dockwerk/filterholder/17636/holder_02.jpg

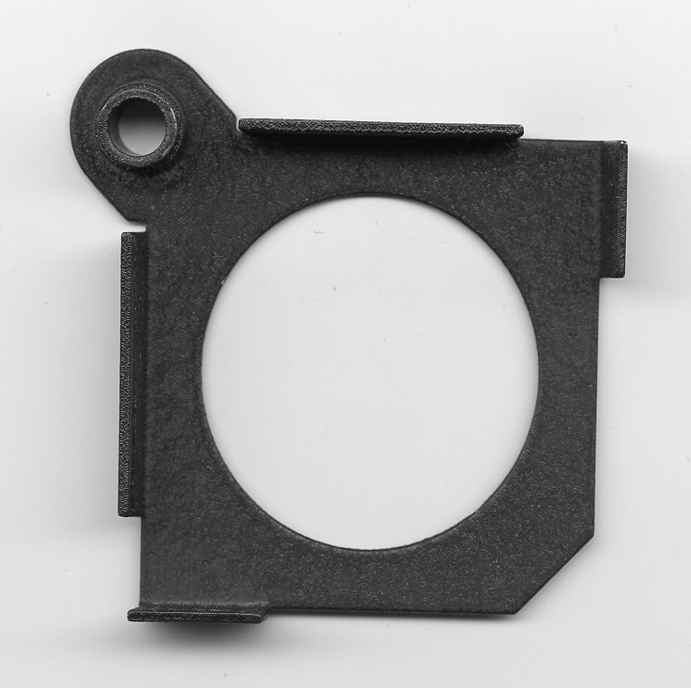
17636/holder_02.jpg
