dockwerk/filterholder/17636/holder_screw_correct.jpg

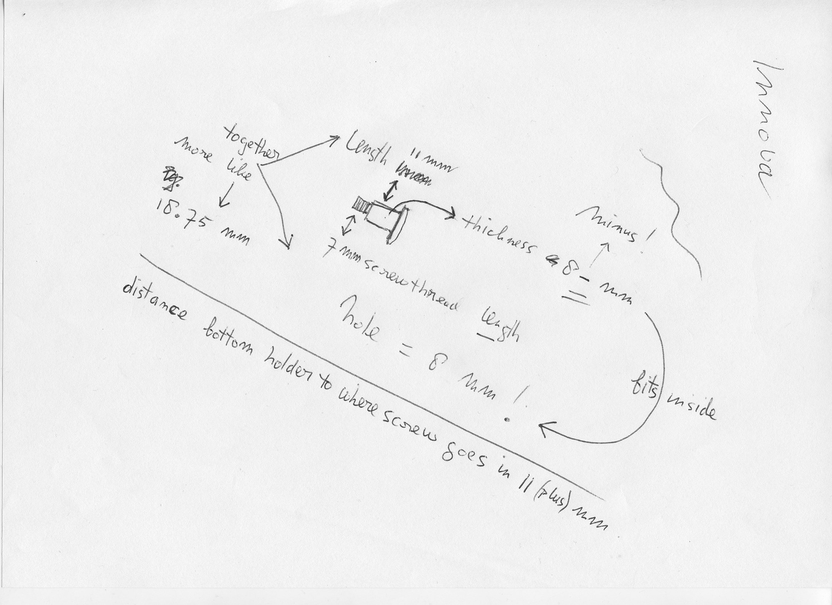
17636/holder_screw_correct.jpg
