dockwerk/filterholder/17636/holder_with_screw.jpg

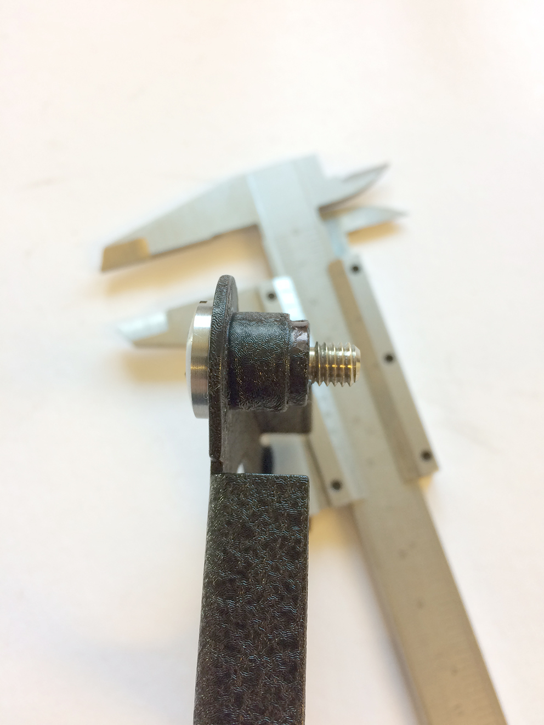
17636/holder_with_screw.jpg
