dockwerk/filterholder/prototypes/DSC_9276.jpg

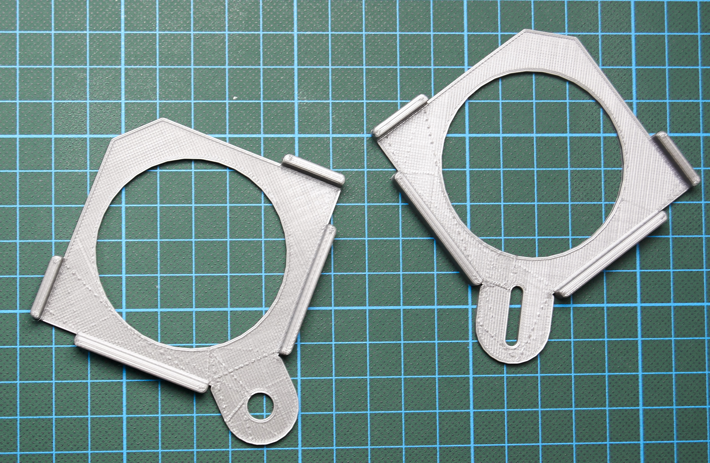
prototypes/DSC_9276.jpg
