dockwerk/filterholder/prototypes/DSC_9277.jpg

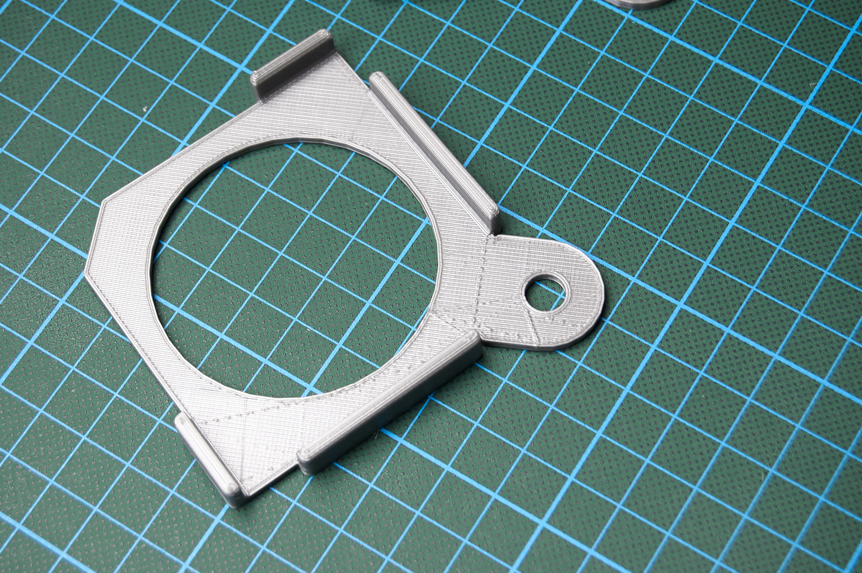
prototypes/DSC_9277.jpg
