dockwerk/filterholder/prototypes/DSC_9278.jpg

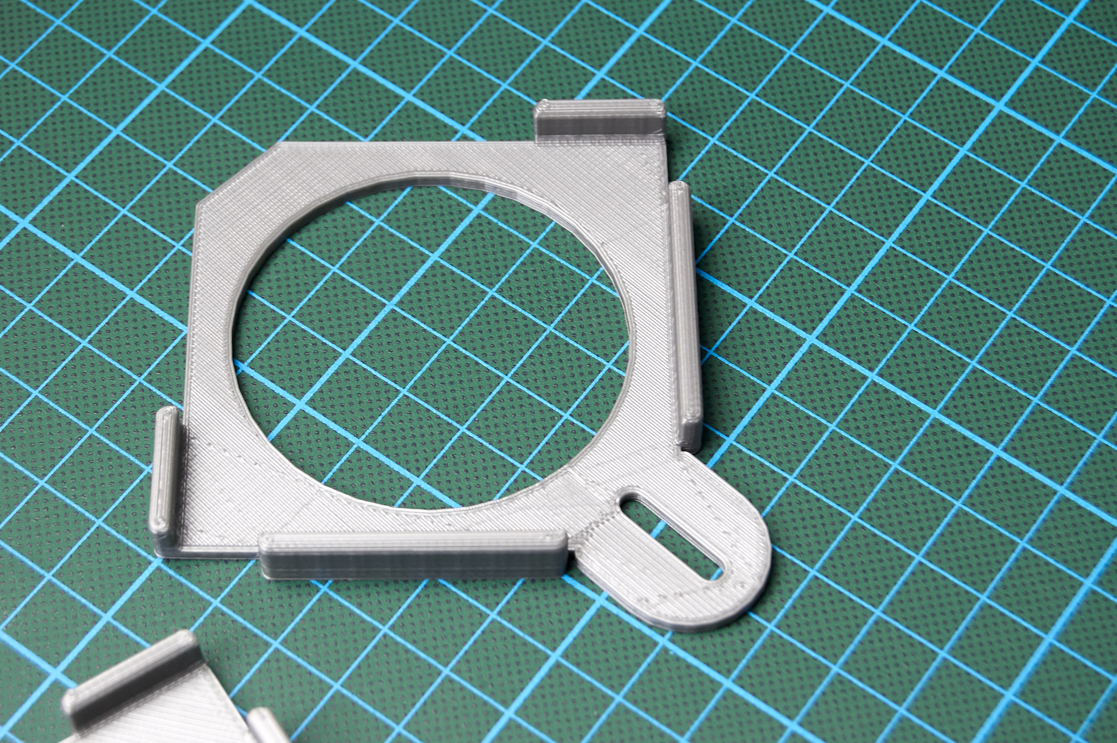
prototypes/DSC_9278.jpg
