dockwerk/filterholder/prototypes/DSC_9281.jpg

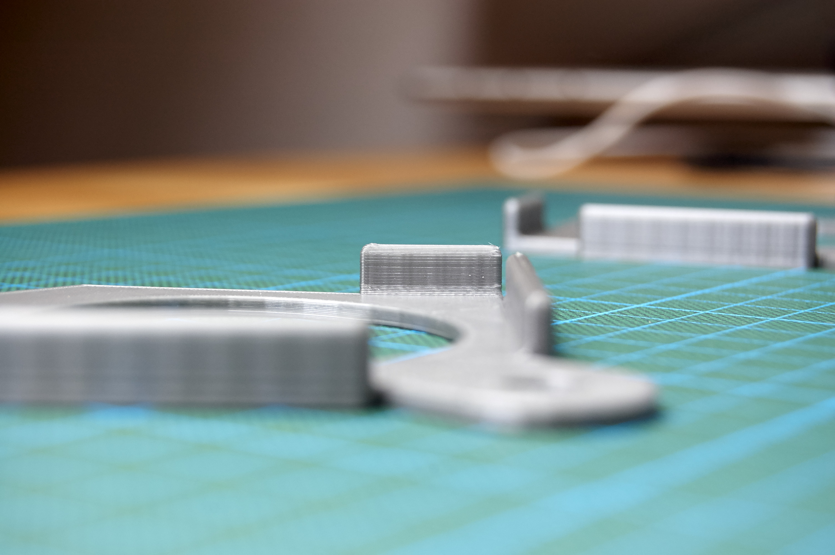
prototypes/DSC_9281.jpg
