dockwerk/filterholder/prototypes/DSC_9283.jpg

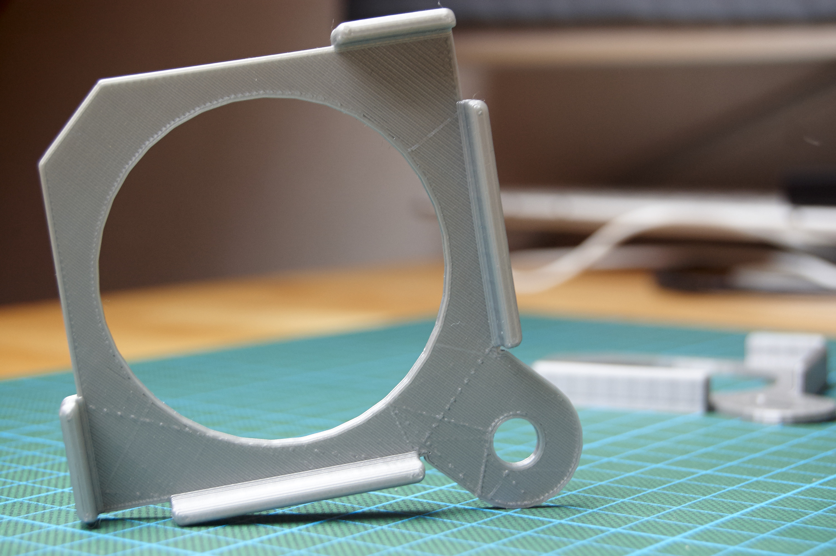
prototypes/DSC_9283.jpg
