dockwerk/filterholder/17636/holder_03_screw_measurements_off.jpg

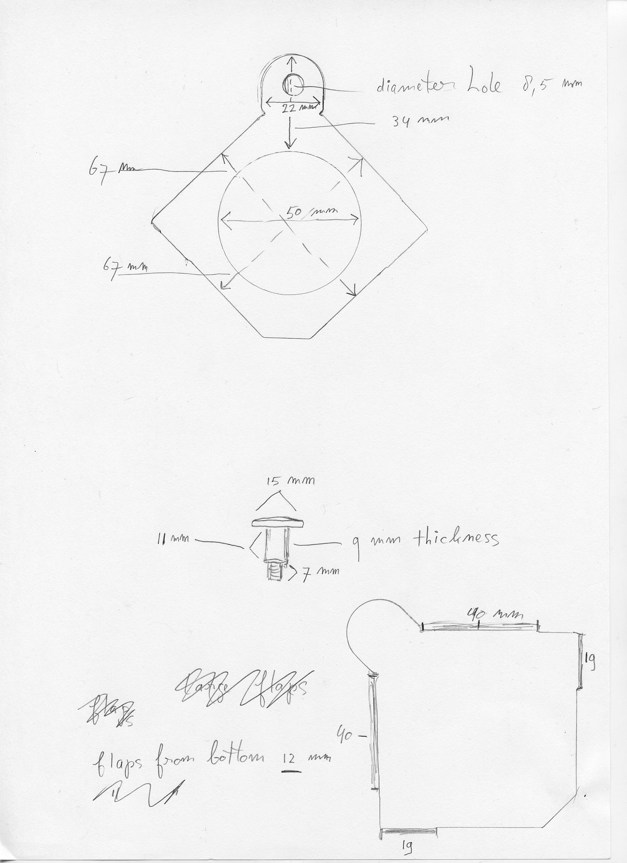
17636/holder_03_screw_measurements_off.jpg
